mike-rankin/ESP32_Particle_Sensor/Images/IMG_1927.jpg

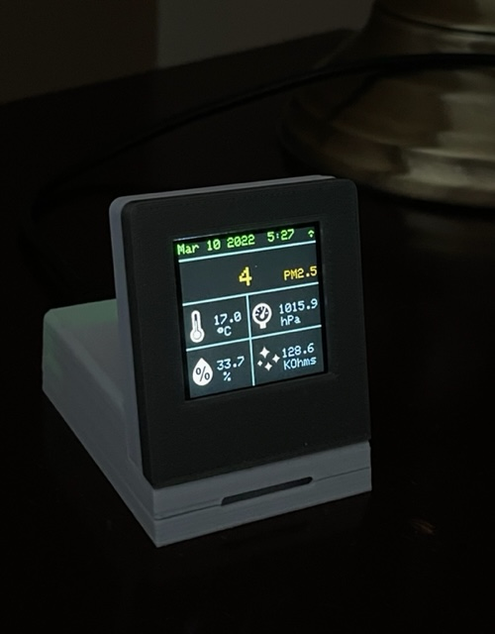
Images/IMG_1927.jpg
